JordanAceto/msm_stereo_LPF/circuit_boards/envelope_follower/docs/2D/envelope_follower_B.Cu.pdf

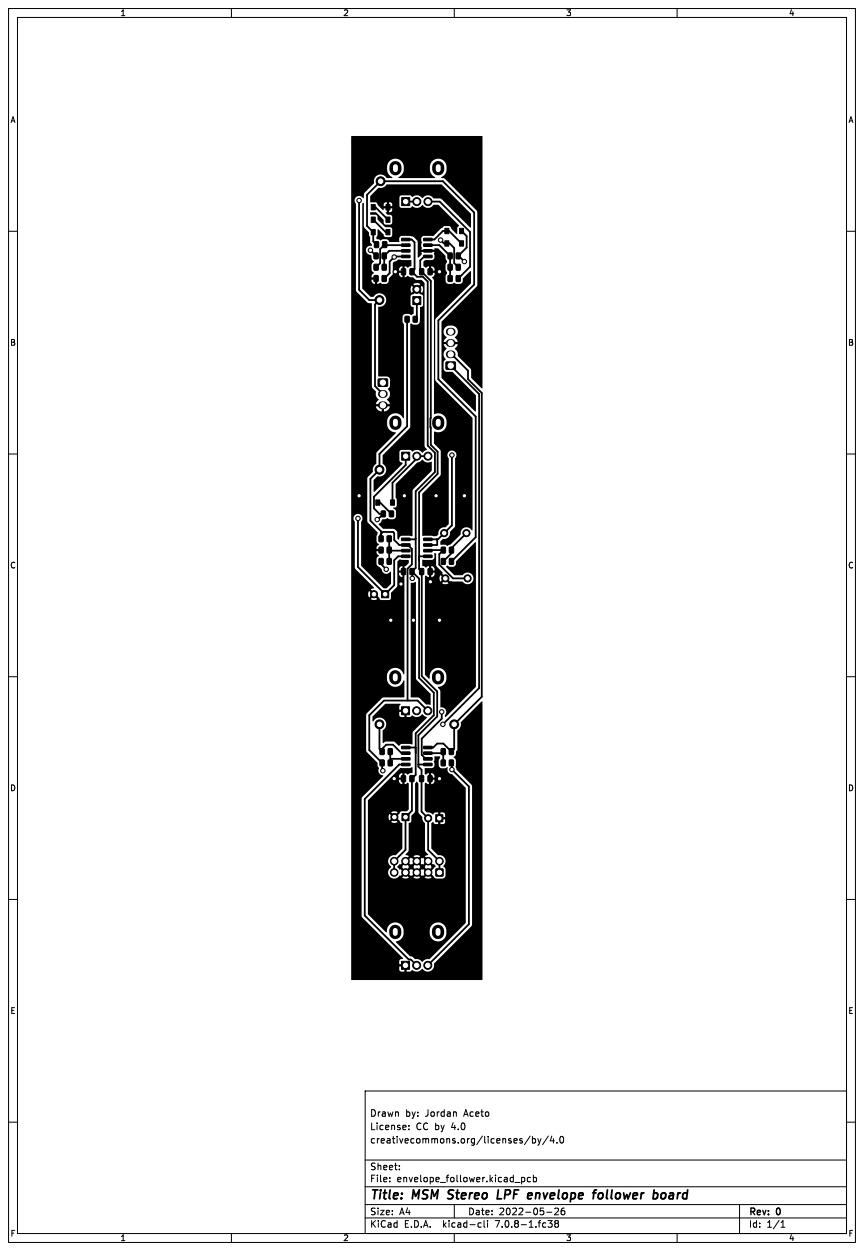
[picture p38: page 1]

File: envelope_follower.kicad_pcb Sheet: creativecommons.org/licenses/by/4.0

Id: 1/1 Title: MSM Stereo LPF envelope follower board
