JordanAceto/msm_stereo_LPF/circuit_boards/LFO_and_PS/docs/2D/lfo_and_power_supply_B.SilkS.pdf

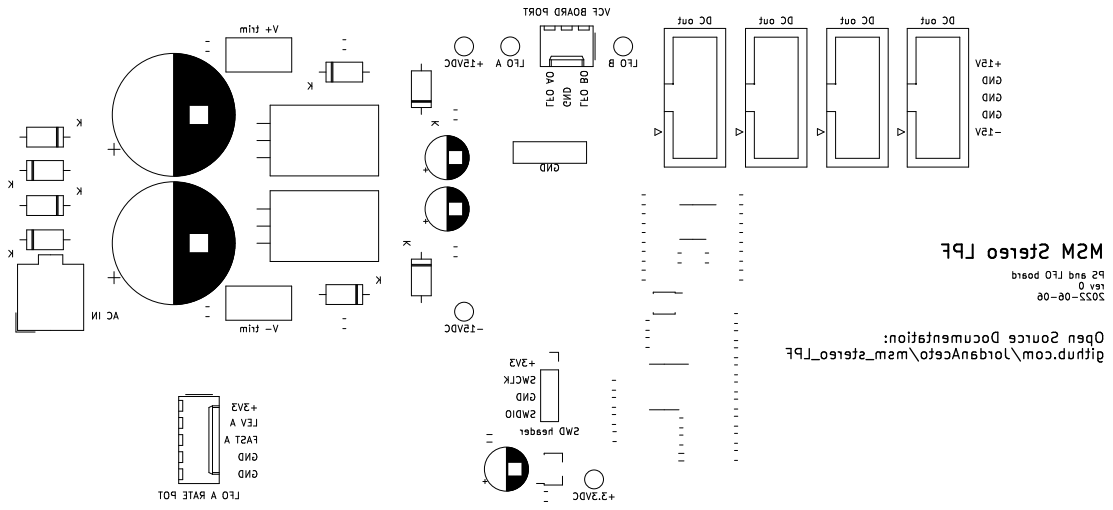
[picture p40: page 1]

PS and LFO board
rev 0

Open Source Documentation: github.com/JordanAceto/msm_stereo_LPF

File: lfo_and_power_supply.kicad_pcb Sheet: creativecommons.org/licences/by/4.0

Id: 1/1 Title: MSS Stereo LPF PS and LFO board
