JordanAceto/msm_stereo_LPF/circuit_boards/lowpass_filters/docs/2D/filter_board_B.SilkS.pdf

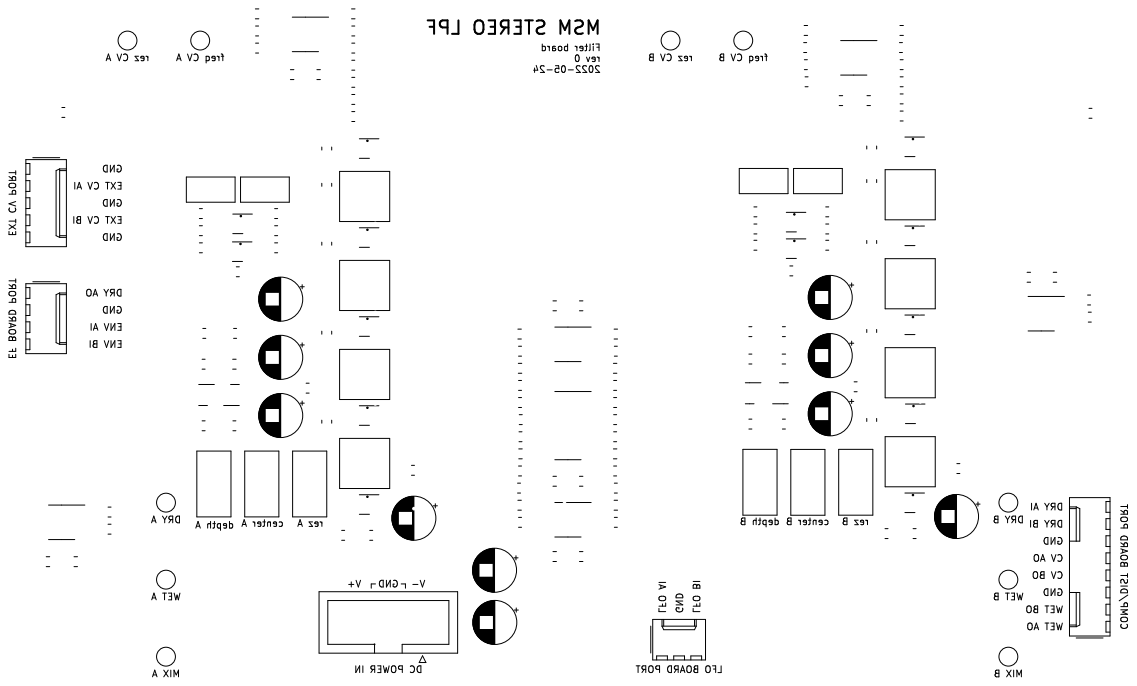
[picture p44: page 1]

EXT CV AI MIX A
DRY AI GND

Id: 1/1 Title: MSM Stereo LPF filter board
