JordanAceto/msm_stereo_LPF/circuit_boards/lowpass_filters/docs/2D/filter_board_Edge.Cuts.pdf

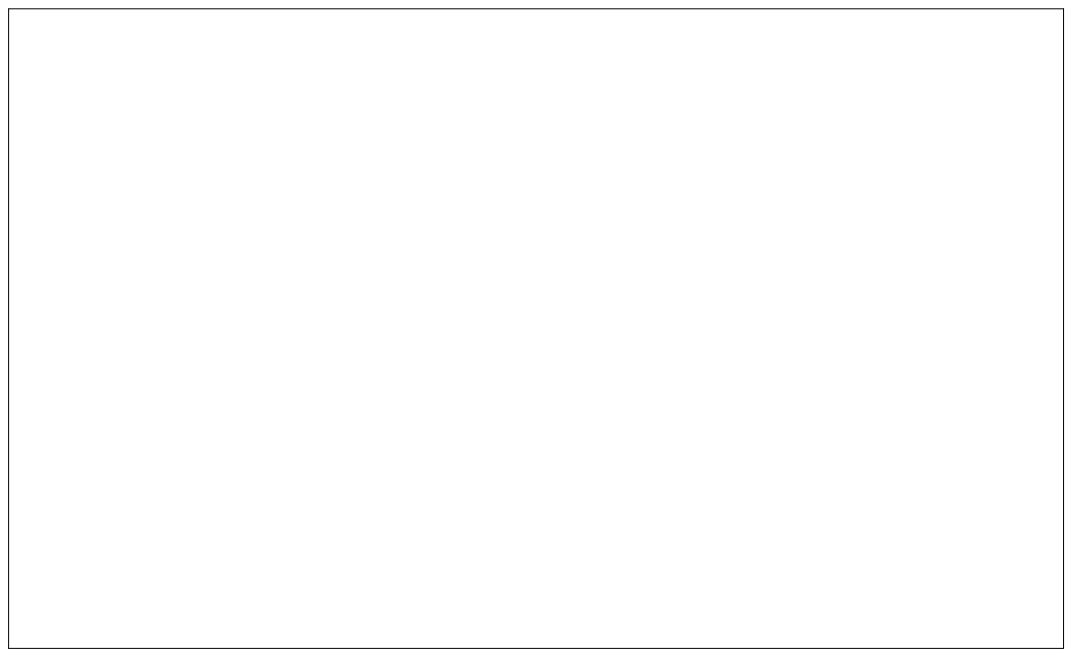
[picture p45: page 1]

Id: 1/1 Title: MSM Stereo LPF filter board
