JordanAceto/msm_stereo_LPF/circuit_boards/lowpass_filters/docs/2D/filter_board_F.Paste.pdf

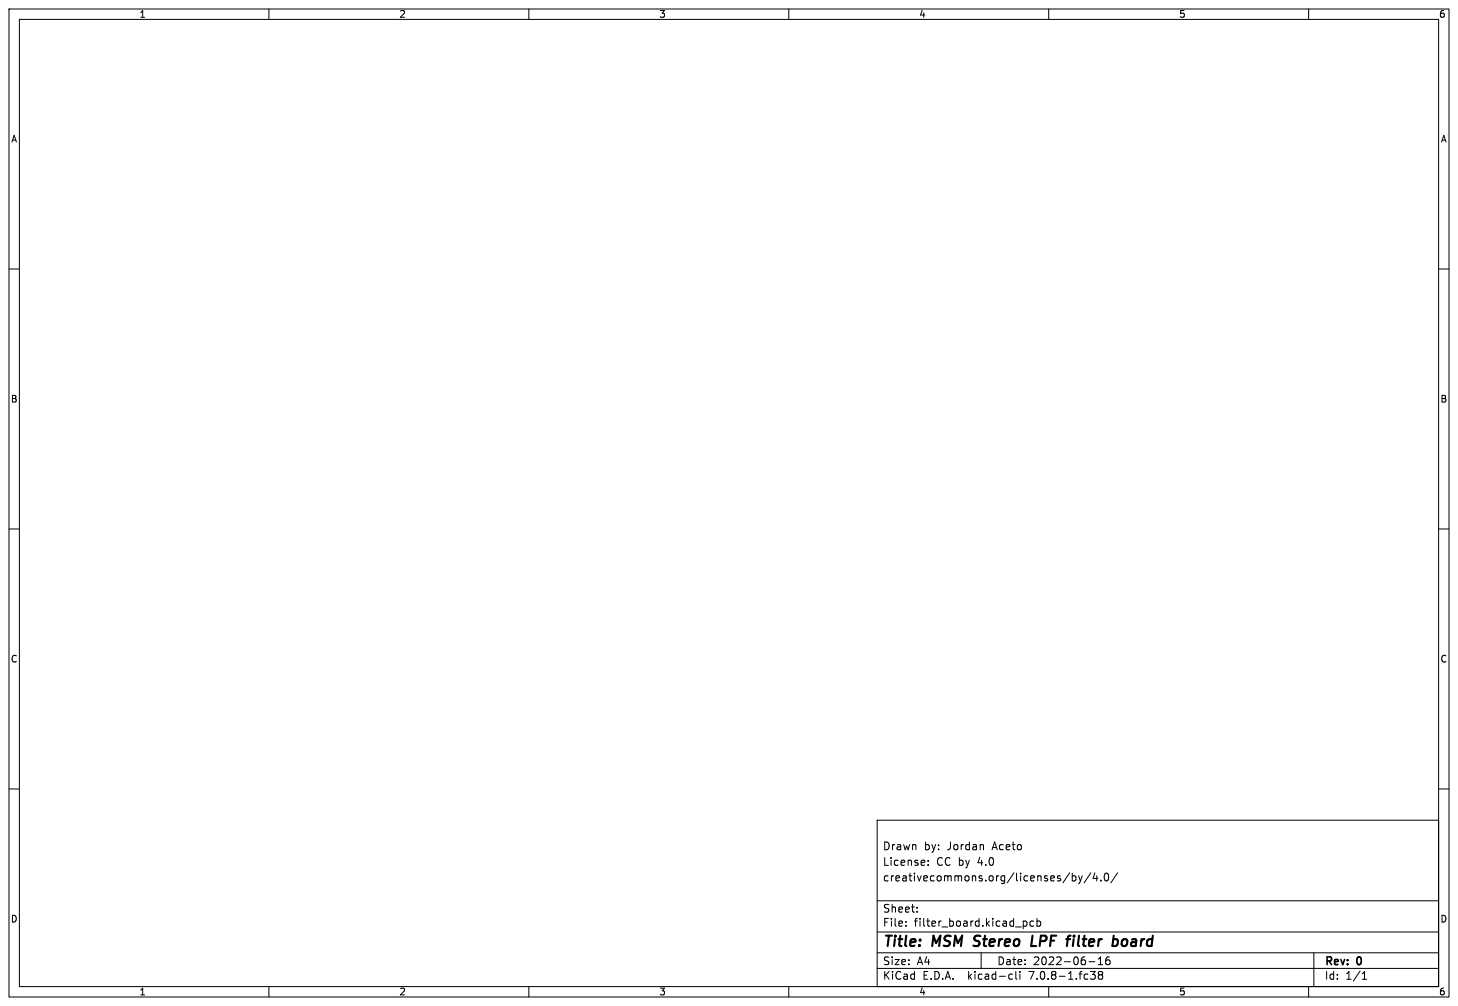
[picture p48: page 1]

Id: 1/1 Title: MSM Stereo LPF filter board
