JordanAceto/msm_stereo_LPF/circuit_boards/lowpass_filters/docs/2D/filter_board_In2.Cu.pdf

Id: 1/1 Title: MSM Stereo LPF filter board
