JordanAceto/msm_stereo_LPF/firmware/BSP/BSP_DMA.cpp

#include "BSP_ADC1.hpp"
#include "BSP_DMA.hpp"
#include "stm32l031xx.h"

namespace BSP::dma
{
    void init()
    {
        // enable DMA clock access
        RCC->AHBENR |= RCC_AHBENR_DMA1EN;

        // set circular mode, mem & periph size to 16 bits, increment memory
        DMA1_Channel1->CCR |= DMA_CCR_CIRC | DMA_CCR_MSIZE_0 | DMA_CCR_PSIZE_0 | DMA_CCR_MINC;

        // DMA transfer length
        DMA1_Channel1->CNDTR = BSP::adc1::NUM_INPUTS;

        // set peripheral address to ADC1 Data Register
        DMA1_Channel1->CPAR = (uint32_t)&(ADC1->DR);

        // set memory address to the array of raw adc readings
        DMA1_Channel1->CMAR = (uint32_t)BSP::adc1::getPtrToRawInputArray();

        // enable DMA1 channel 1
        DMA1_Channel1->CCR |= DMA_CCR_EN;
    }
}
